silardg/SoM-STM32F4/SoM-STM32F4/Docs/3rdLayer.PNG

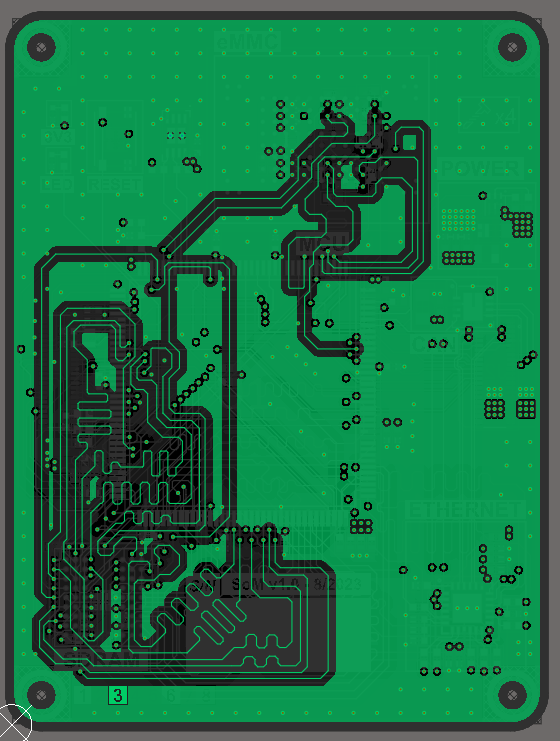
SoM-STM32F4/Docs/3rdLayer.PNG
