silardg/SoM-STM32F4/SoM-STM32F4/Docs/5thLayer.PNG

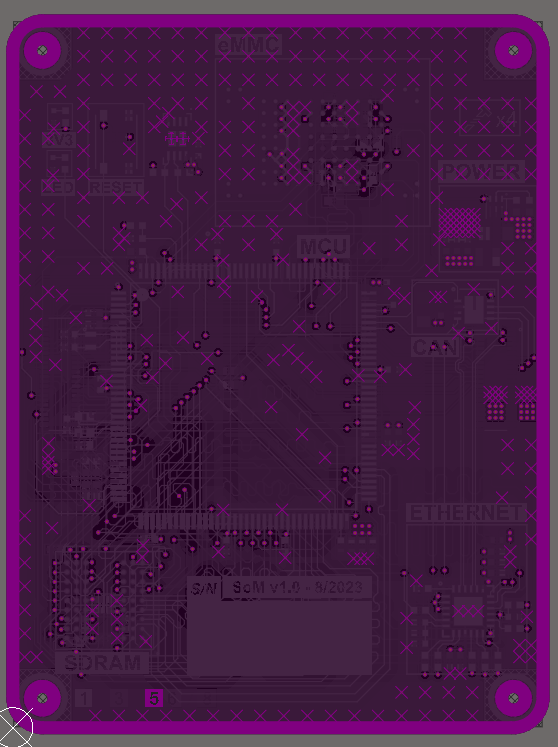
SoM-STM32F4/Docs/5thLayer.PNG
