silardg/SoM-STM32F4/SoM-STM32F4/Docs/6thLayer.PNG

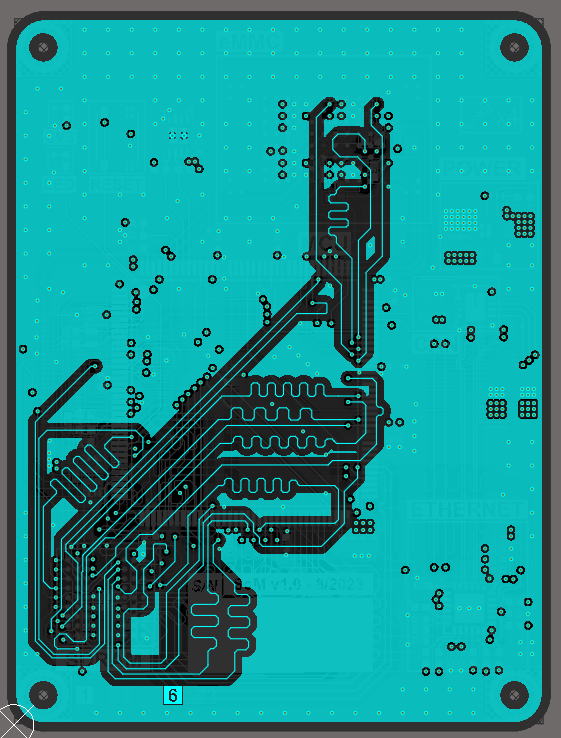
SoM-STM32F4/Docs/6thLayer.PNG
